sbkirby/RPi_bird_feeder_monitor/images/RPi Camera Outside View.jpg

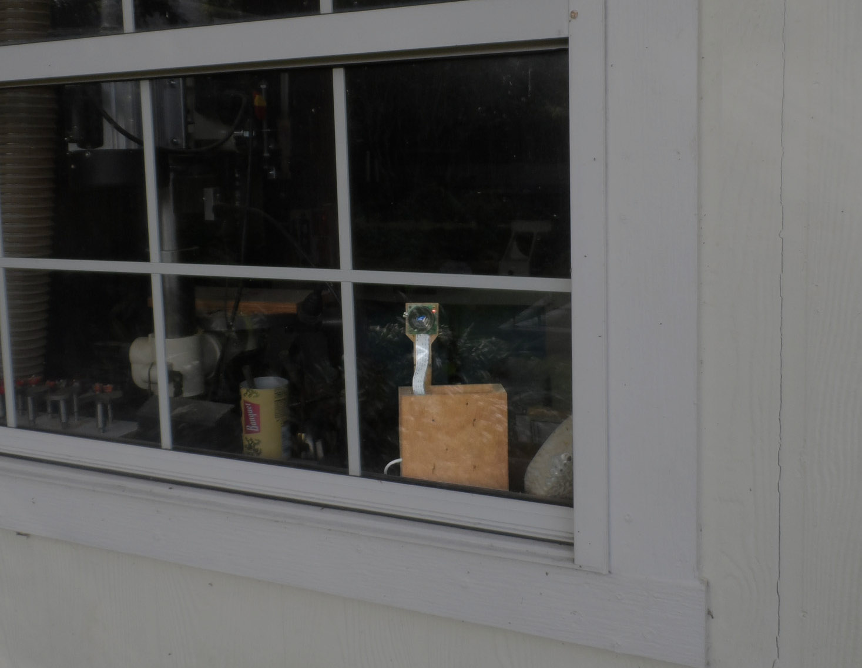
images/RPi Camera Outside View.jpg
