sbkirby/RPi_bird_feeder_monitor/images/RPi_3 Stuff.jpg

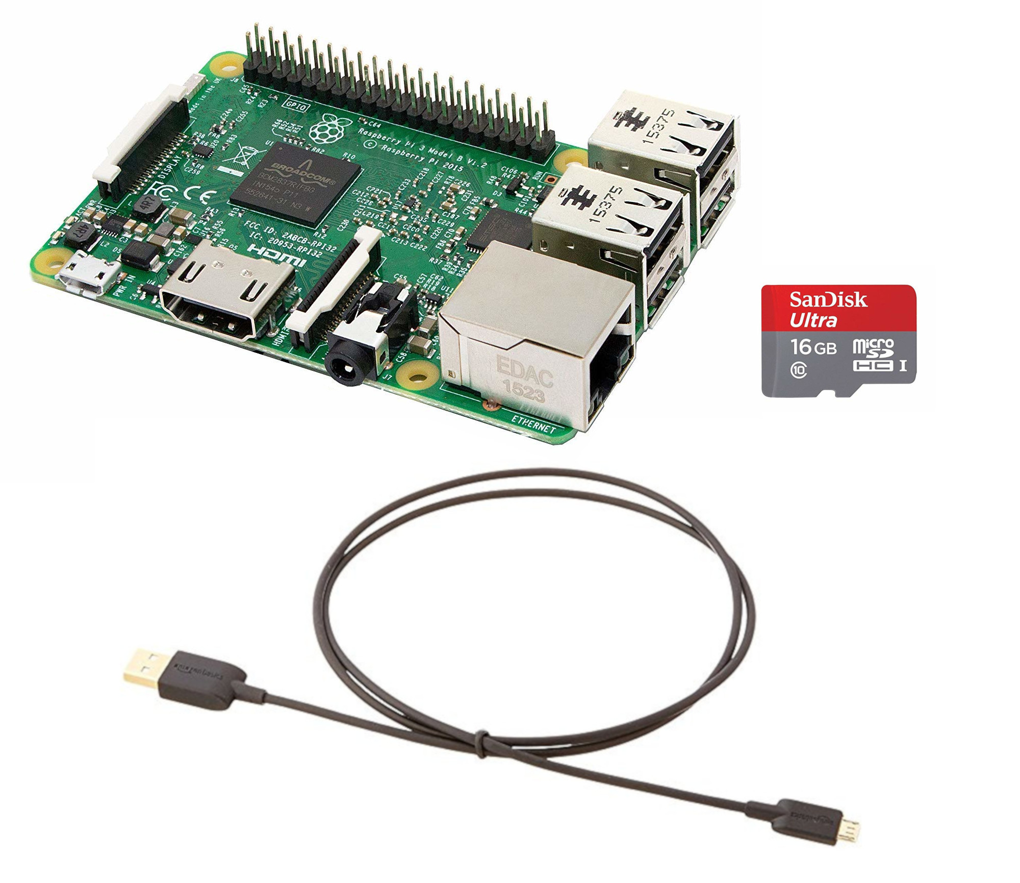
images/RPi_3 Stuff.jpg
